KennyNeutron/AeroTech/Docs/KiCAD Files/AeroTech/AeroTech.kicad_pcb

## KiCad design modern-keyboard.kicad_pcb

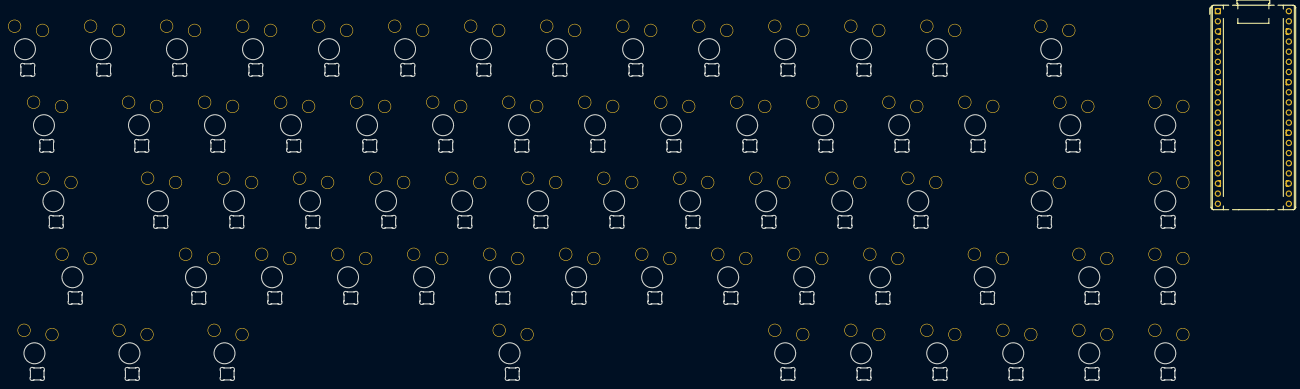
[picture p5: board modern-keyboard.kicad_pcb from above]

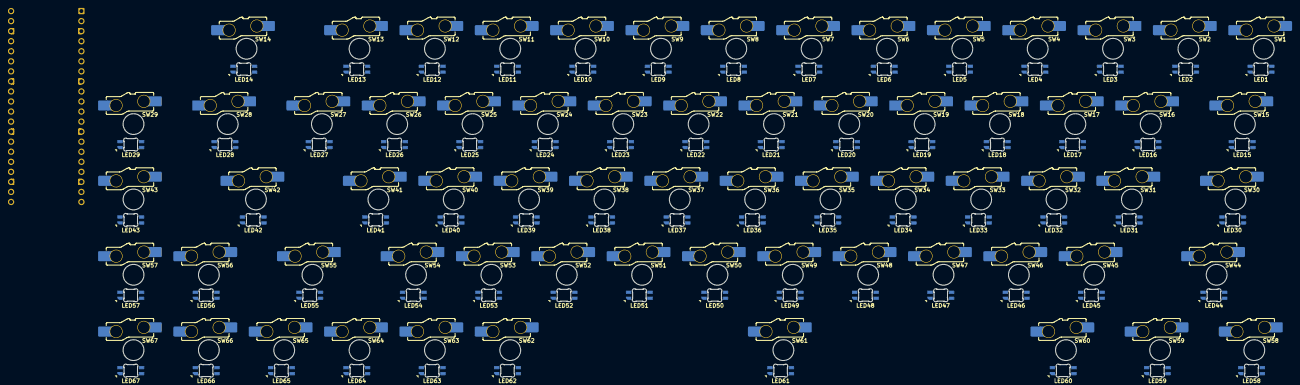
[picture p6: board modern-keyboard.kicad_pcb from below]

Board: 2 copper layers, 135 parts (134 on the bottom side), 84 nets, no tracks yet.

Parts:
A1: RaspberryPi_Pico; RaspberryPi_Pico_Common_THT
LED1, LED2, LED3, LED4, LED5, LED6, LED7, LED8, LED9, LED10, LED11, LED12, LED13, LED14, LED15, LED16, LED17, LED18, LED19, LED20, LED21, LED22, LED23, LED24, LED25, LED26, LED27, LED28, LED29, LED30, LED31, LED32, LED33, LED34, LED35, LED36, LED37, LED38, LED39, LED40, LED41, LED42, LED43, LED44, LED45, LED46, LED47, LED48, LED49, LED50, LED51, LED52, LED53, LED54, LED55, LED56, LED57, LED58, LED59, LED60, LED61, LED62, LED63, LED64, LED65, LED66, LED67: SK6812MINI-E; LED_KS33_6028R
SW1, SW2, SW3, SW4, SW5, SW6, SW7, SW8, SW9, SW10, SW11, SW12, SW13, SW16, SW17, SW18, SW19, SW20, SW21, SW22, SW23, SW24, SW25, SW26, SW27, SW29, SW31, SW32, SW33, SW34, SW35, SW36, SW37, SW38, SW39, SW40, SW41, SW43, SW45, SW46, SW47, SW48, SW49, SW50, SW51, SW52, SW53, SW54, SW56, SW57, SW62, SW63, SW64, SW65, SW66, SW67: SW_Push_45deg; SW_KS33_HS_KS-2P02B01-02_HS_1u
SW14: SW_Push_45deg; SW_KS33_HS_KS-2P02B01-02_HS_2u
SW15, SW28: SW_Push_45deg; SW_KS33_HS_KS-2P02B01-02_1.5u
SW30, SW55: SW_Push_45deg; SW_KS33_HS_KS-2P02B01-02_1.75u
SW42, SW44: SW_Push_45deg; SW_KS33_HS_KS-2P02B01-02_HS_2.25u
SW58, SW59, SW60: SW_Push_45deg; SW_KS33_HS_KS-2P02B01-02_1.25u
SW61: SW_Push_45deg; SW_KS33_HS_KS-2P02B01-02_HS_6.25u

Connections:
+5V: A1.40 (VBUS), LED1.1 (VDD), LED2.1 (VDD), LED3.1 (VDD), LED4.1 (VDD), LED5.1 (VDD), LED6.1 (VDD), LED7.1 (VDD), LED8.1 (VDD), LED9.1 (VDD), LED10.1 (VDD), LED11.1 (VDD), LED12.1 (VDD), LED13.1 (VDD), LED14.1 (VDD), LED15.1 (VDD), LED16.1 (VDD), LED17.1 (VDD), LED18.1 (VDD), LED19.1 (VDD), LED20.1 (VDD), LED21.1 (VDD), LED22.1 (VDD), LED23.1 (VDD), LED24.1 (VDD), LED25.1 (VDD), LED26.1 (VDD), LED27.1 (VDD), LED28.1 (VDD), LED29.1 (VDD), LED30.1 (VDD), LED31.1 (VDD), LED32.1 (VDD), LED33.1 (VDD), LED34.1 (VDD), LED35.1 (VDD), LED36.1 (VDD), LED37.1 (VDD), LED38.1 (VDD), LED39.1 (VDD), LED40.1 (VDD), LED41.1 (VDD), LED42.1 (VDD), LED43.1 (VDD), LED44.1 (VDD), LED45.1 (VDD), LED46.1 (VDD), LED47.1 (VDD), LED48.1 (VDD), LED49.1 (VDD), LED50.1 (VDD), LED51.1 (VDD), LED52.1 (VDD), LED53.1 (VDD), LED54.1 (VDD), LED55.1 (VDD), LED56.1 (VDD), LED57.1 (VDD), LED58.1 (VDD), LED59.1 (VDD), LED60.1 (VDD), LED61.1 (VDD), LED62.1 (VDD), LED63.1 (VDD), LED64.1 (VDD), LED65.1 (VDD), LED66.1 (VDD), LED67.1 (VDD)
Col 0: A1.1 (GPIO0), SW1.1, SW15.1, SW30.1, SW44.1, SW57.1
Col 1: A1.2 (GPIO1), SW2.1, SW16.1, SW31.1, SW45.1, SW59.1
Col 2: A1.4 (GPIO2), SW3.1, SW17.1, SW32.1, SW46.1, SW60.1
Col 3: A1.5 (GPIO3), SW4.1, SW18.1, SW33.1, SW47.1
Col 4: A1.6 (GPIO4), SW5.1, SW19.1, SW34.1, SW48.1
Col 5: A1.7 (GPIO5), SW6.1, SW20.1, SW35.1, SW49.1, SW61.1
Col 6: A1.9 (GPIO6), SW7.1, SW21.1, SW36.1, SW50.1
Col 7: A1.10 (GPIO7), SW8.1, SW22.1, SW37.1, SW51.1
Col 8: A1.11 (GPIO8), SW9.1, SW23.1, SW38.1, SW52.1
Col 9: A1.12 (GPIO9), SW10.1, SW24.1, SW39.1, SW53.1, SW62.1
Col 10: A1.14 (GPIO10), SW11.1, SW25.1, SW40.1, SW54.1, SW63.1
Col 11: A1.15 (GPIO11), SW12.1, SW26.1, SW41.1, SW64.1
Col 12: A1.16 (GPIO12), SW13.1, SW27.1, SW55.1, SW65.1
Col 13: A1.17 (GPIO13), SW14.1, SW28.1, SW42.1, SW56.1, SW66.1
Col 14: A1.19 (GPIO14), SW29.1, SW43.1, SW58.1, SW67.1
GND: A1.3 (GND), A1.8 (GND), A1.13 (GND), A1.18 (GND), A1.23 (GND), A1.28 (GND), A1.38 (GND), LED1.4 (VSS), LED2.4 (VSS), LED3.4 (VSS), LED4.4 (VSS), LED5.4 (VSS), LED6.4 (VSS), LED7.4 (VSS), LED8.4 (VSS), LED9.4 (VSS), LED10.4 (VSS), LED11.4 (VSS), LED12.4 (VSS), LED13.4 (VSS), LED14.4 (VSS), LED15.4 (VSS), LED16.4 (VSS), LED17.4 (VSS), LED18.4 (VSS), LED19.4 (VSS), LED20.4 (VSS), LED21.4 (VSS), LED22.4 (VSS), LED23.4 (VSS), LED24.4 (VSS), LED25.4 (VSS), LED26.4 (VSS), LED27.4 (VSS), LED28.4 (VSS), LED29.4 (VSS), LED30.4 (VSS), LED31.4 (VSS), LED32.4 (VSS), LED33.4 (VSS), LED34.4 (VSS), LED35.4 (VSS), LED36.4 (VSS), LED37.4 (VSS), LED38.4 (VSS), LED39.4 (VSS), LED40.4 (VSS), LED41.4 (VSS), LED42.4 (VSS), LED43.4 (VSS), LED44.4 (VSS), LED45.4 (VSS), LED46.4 (VSS), LED47.4 (VSS), LED48.4 (VSS), LED49.4 (VSS), LED50.4 (VSS), LED51.4 (VSS), LED52.4 (VSS), LED53.4 (VSS), LED54.4 (VSS), LED55.4 (VSS), LED56.4 (VSS), LED57.4 (VSS), LED58.4 (VSS), LED59.4 (VSS), LED60.4 (VSS), LED61.4 (VSS), LED62.4 (VSS), LED63.4 (VSS), LED64.4 (VSS), LED65.4 (VSS), LED66.4 (VSS), LED67.4 (VSS)
unnamed: LED1.2 (DOUT), LED2.3 (DIN)
unnamed: LED2.2 (DOUT), LED3.3 (DIN)
unnamed: LED3.2 (DOUT), LED4.3 (DIN)
unnamed: LED4.2 (DOUT), LED5.3 (DIN)
unnamed: LED5.2 (DOUT), LED6.3 (DIN)
unnamed: LED6.2 (DOUT), LED7.3 (DIN)
unnamed: LED7.2 (DOUT), LED8.3 (DIN)
unnamed: LED8.2 (DOUT), LED9.3 (DIN)
unnamed: LED9.2 (DOUT), LED10.3 (DIN)
unnamed: LED10.2 (DOUT), LED11.3 (DIN)
unnamed: LED11.2 (DOUT), LED12.3 (DIN)
unnamed: LED12.2 (DOUT), LED13.3 (DIN)
unnamed: LED13.2 (DOUT), LED14.3 (DIN)
unnamed: LED14.2 (DOUT), LED15.3 (DIN)
unnamed: LED15.2 (DOUT), LED16.3 (DIN)
unnamed: LED16.2 (DOUT), LED17.3 (DIN)
unnamed: LED17.2 (DOUT), LED18.3 (DIN)
unnamed: LED18.2 (DOUT), LED19.3 (DIN)
unnamed: LED19.2 (DOUT), LED20.3 (DIN)
unnamed: LED20.2 (DOUT), LED21.3 (DIN)
unnamed: LED21.2 (DOUT), LED22.3 (DIN)
unnamed: LED22.2 (DOUT), LED23.3 (DIN)
unnamed: LED23.2 (DOUT), LED24.3 (DIN)
unnamed: LED24.2 (DOUT), LED25.3 (DIN)
unnamed: LED25.2 (DOUT), LED26.3 (DIN)
unnamed: LED26.2 (DOUT), LED27.3 (DIN)
unnamed: LED27.2 (DOUT), LED28.3 (DIN)
unnamed: LED28.2 (DOUT), LED29.3 (DIN)
unnamed: LED29.2 (DOUT), LED30.3 (DIN)
unnamed: LED30.2 (DOUT), LED31.3 (DIN)
unnamed: LED31.2 (DOUT), LED32.3 (DIN)
unnamed: LED32.2 (DOUT), LED33.3 (DIN)
unnamed: LED33.2 (DOUT), LED34.3 (DIN)
unnamed: LED34.2 (DOUT), LED35.3 (DIN)
unnamed: LED35.2 (DOUT), LED36.3 (DIN)
unnamed: LED36.2 (DOUT), LED37.3 (DIN)
unnamed: LED37.2 (DOUT), LED38.3 (DIN)
unnamed: LED38.2 (DOUT), LED39.3 (DIN)
unnamed: LED39.2 (DOUT), LED40.3 (DIN)
unnamed: LED40.2 (DOUT), LED41.3 (DIN)
unnamed: LED41.2 (DOUT), LED42.3 (DIN)
unnamed: LED42.2 (DOUT), LED43.3 (DIN)
unnamed: LED43.2 (DOUT), LED44.3 (DIN)
unnamed: LED44.2 (DOUT), LED45.3 (DIN)
unnamed: LED45.2 (DOUT), LED46.3 (DIN)
unnamed: LED46.2 (DOUT), LED47.3 (DIN)
unnamed: LED47.2 (DOUT), LED48.3 (DIN)
unnamed: LED48.2 (DOUT), LED49.3 (DIN)
unnamed: LED49.2 (DOUT), LED50.3 (DIN)
unnamed: LED50.2 (DOUT), LED51.3 (DIN)
unnamed: LED51.2 (DOUT), LED52.3 (DIN)
unnamed: LED52.2 (DOUT), LED53.3 (DIN)
unnamed: LED53.2 (DOUT), LED54.3 (DIN)
unnamed: LED54.2 (DOUT), LED55.3 (DIN)
unnamed: LED55.2 (DOUT), LED56.3 (DIN)
unnamed: LED56.2 (DOUT), LED57.3 (DIN)
unnamed: LED57.2 (DOUT), LED58.3 (DIN)
unnamed: LED58.2 (DOUT), LED59.3 (DIN)
unnamed: LED59.2 (DOUT), LED60.3 (DIN)
unnamed: LED60.2 (DOUT), LED61.3 (DIN)
unnamed: LED61.2 (DOUT), LED62.3 (DIN)
unnamed: LED62.2 (DOUT), LED63.3 (DIN)
unnamed: LED63.2 (DOUT), LED64.3 (DIN)
unnamed: LED64.2 (DOUT), LED65.3 (DIN)
unnamed: LED65.2 (DOUT), LED66.3 (DIN)
unnamed: LED66.2 (DOUT), LED67.3 (DIN)
RGB: A1.20 (GPIO15), LED1.3 (DIN)
