KennyNeutron/AeroTech/Code/Embedded/AeroTech_Sensor/AeroTech_Sensor.ino

#include <Wire.h>
#include "RTClib.h"
#include "DataStructure.h"
#include <ph4502c_sensor.h>
#include <DHT.h>

//Water Level Sensor
#define WaterLevel_Low 3
#define WaterLevel_Mid 4
#define WaterLevel_High 5

RTC_DS3231 RTC;

// ---- DHT setup ----
#define DHTPIN 6
#define DHTTYPE DHT11
DHT dht(DHTPIN, DHTTYPE);

//TDS
#define TdsSensorPin A0

//PH
#define PH4502C_PH_LEVEL_PIN A1
#define PH4502C_TEMP_PIN A2

PH4502C_Sensor ph4502(PH4502C_PH_LEVEL_PIN, PH4502C_TEMP_PIN);

// Constants
const float VREF = 5.0;    // Reference voltage (Arduino Nano = 5V)
const int SCOUNT = 30;     // Sample count for averaging
int analogBuffer[SCOUNT];  // Buffer to store samples
int analogBufferIndex = 0;
float averageVoltage = 0;
float tdsValue = 0;
bool TDS_INIT = false;

// Safe read with timeout (prevents stalls)
bool readDHTSafe(float &tC, float &h, uint16_t timeout_ms = 2500) {
  uint32_t t0 = millis();
  do {
    h = dht.readHumidity();
    tC = dht.readTemperature();  // Celsius
    if (!isnan(h) && !isnan(tC)) return true;
    delay(100);
  } while (millis() - t0 < timeout_ms);
  return false;
}

void setup() {
  Serial.begin(115200);

  if (!RTC.begin()) {
    Serial.println("Couldn't find RTC");
    while (1)
      ;
  }

  if (RTC.lostPower()) {
    Serial.println("RTC lost power, setting the time...");

    // Set the date and time (Year, Month, Day, Hour, Minute, Second)
    RTC.adjust(DateTime(2025, 9, 12, 11, 45, 0));
    // Example: 2025-09-12 11:45:00
  }


  Serial.println("AeroTech Dummy Data Sender Ready...");

  dht.begin(); // Initialize DHT sensor

  // Fill struct with dummy values
  Data_AeroTech.Header = 0x55;  // Example header
  Data_AeroTech.AD_Time_HH = 0;
  Data_AeroTech.AD_Time_MM = 0;
  Data_AeroTech.AD_Time_SS = 0;
  Data_AeroTech.AD_pH = 6.8;
  Data_AeroTech.AD_TDS = 750.5;
  Data_AeroTech.AD_WaterLevel = 0;
  Data_AeroTech.AD_Temperature = 0.0;
  Data_AeroTech.Footer = 0xAA;  // Example footer

  WaterLevelSensor_setup();

  // Initialize the PH4502 instance
  ph4502.init();
}

void loop() {

  DateTime RTC_Now = RTC.now();
  TDS_loop();

  float tC = 0.0;
  float h = 0.0;
  bool ok = readDHTSafe(tC, h);

  //   // Debug to Serial
  // if (ok) {
  //   Serial.print(F("T="));
  //   Serial.print(tC);
  //   Serial.print(F("C  H="));
  //   Serial.print(h);
  //   Serial.println(F("%"));
  // } else {
  //   Serial.println(F("TIMEOUT: DHT22 not responding"));
  // }

  // Extract time
  Data_AeroTech.AD_Time_HH = RTC_Now.hour();
  Data_AeroTech.AD_Time_MM = RTC_Now.minute();
  Data_AeroTech.AD_Time_SS = RTC_Now.second();

  // Extract date
  Data_AeroTech.AD_DayOfWeek = RTC_Now.dayOfTheWeek();  // 0 = Sunday, 6 = Saturday
  Data_AeroTech.AD_Date_Day = RTC_Now.day();
  Data_AeroTech.AD_Date_Month = RTC_Now.month();
  Data_AeroTech.AD_Date_Year = RTC_Now.year();

  // Temperature from DHT Sensor
  // Temperature from DHT Sensor
  if (!isnan(tC)) {
    Data_AeroTech.AD_Temperature = tC;
  }

  //TDS Value from TDS Sensor
  Data_AeroTech.AD_TDS = tdsValue;

  //pH Value from PH4502C Sensor
  Data_AeroTech.AD_pH = ph4502.read_ph_level();

  // Water Level from Water Level Sensor
  Data_AeroTech.AD_WaterLevel = WaterLevelSensor_Level();


  // Send marker + struct
  Serial.write('A');  // Start marker
  Serial.write((uint8_t *)&Data_AeroTech, sizeof(Data_AeroTech));

  // Debug print to Serial Monitor
  // Serial.print("[Packet Sent] A ");
  // Serial.print("Time: ");
  // Serial.print(Data_AeroTech.AD_Time_HH);
  // Serial.print(":");
  // Serial.print(Data_AeroTech.AD_Time_MM);
  // Serial.print(":");
  // Serial.print(Data_AeroTech.AD_Time_SS);
  // Serial.print(" | Date: ");
  // Serial.print(Data_AeroTech.AD_Date_Year);
  // Serial.print("/");
  // Serial.print(Data_AeroTech.AD_Date_Month);
  // Serial.print("/");
  // Serial.print(Data_AeroTech.AD_Date_Day);
  // Serial.print(" | Day: ");
  // Serial.print(Data_AeroTech.AD_DayOfWeek);

  // Serial.print(" | pH: ");
  // Serial.print(Data_AeroTech.AD_pH);
  // Serial.print(" | TDS: ");
  // Serial.print(Data_AeroTech.AD_TDS);
  // Serial.print(" | Level: ");
  // Serial.print(Data_AeroTech.AD_WaterLevel);
  // Serial.print(" | Temp: ");
  // Serial.println(Data_AeroTech.AD_Temperature);
  delay(3);

  // WaterLevelSensor_Level();
  delay(1000);
}
